rana-sylvatica/OFOF1/Standoffs/Sidewalls/ofof1-walls-3dprint-alt.STL

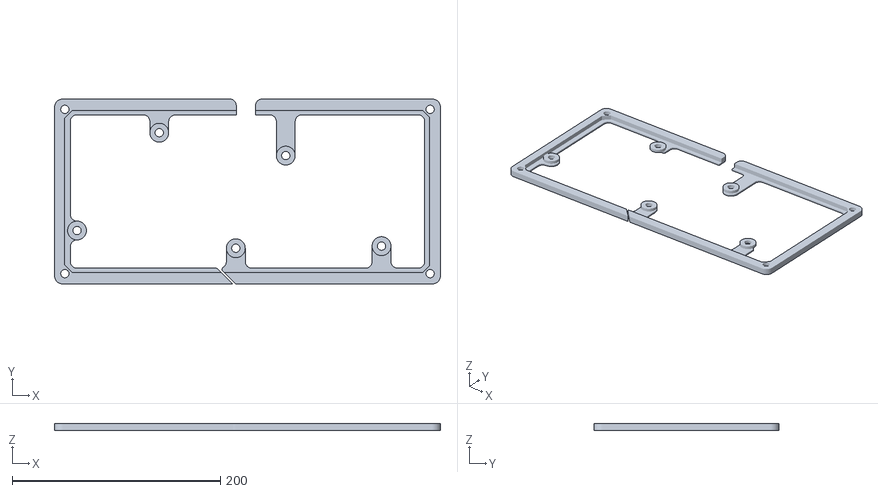
[picture p15: CAD file, 2022-10-11]
Standoffs/Sidewalls/ofof1-walls-3dprint-alt.STL
370.8 x 177.8 x 7.00
