rana-sylvatica/OFOF1/Standoffs/Top_standoff_short.STL

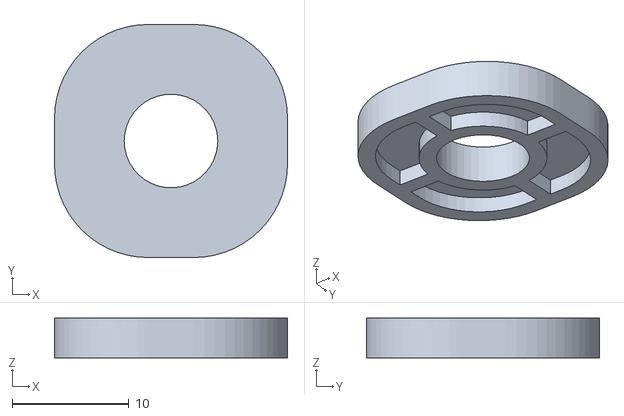
[picture p16: CAD file, 2022-07-05]
Standoffs/Top_standoff_short.STL
19.9 x 19.9 x 3.40
