rana-sylvatica/OFOF1/Standoffs/Sidewalls/ofof1-walls-JLC_acrylic.STL

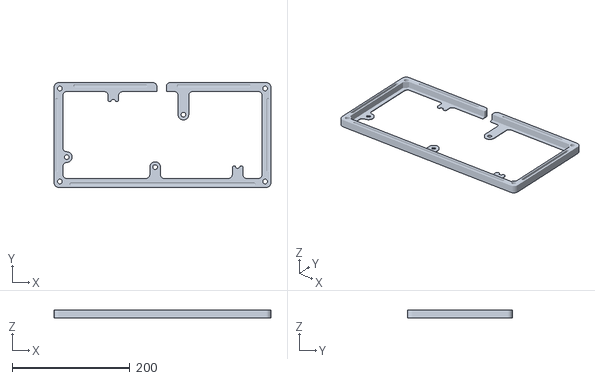
[picture p17: CAD file, 2022-10-11]
Standoffs/Sidewalls/ofof1-walls-JLC_acrylic.STL
368.3 x 177.8 x 13.0
