rana-sylvatica/OFOF1/Standoffs/Bottom_standoff_x10.STL

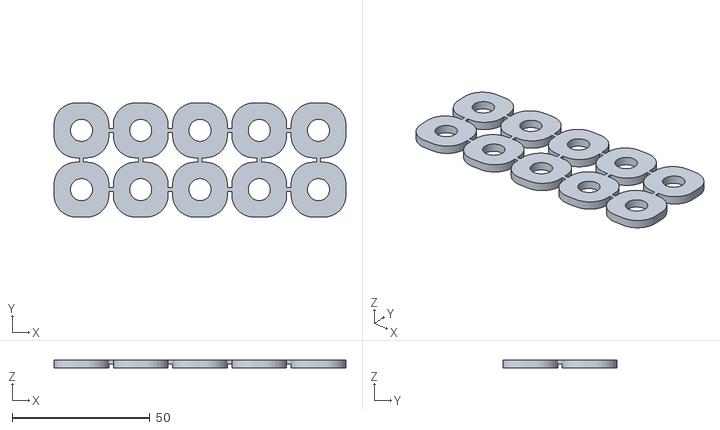
[picture p19: CAD file, 2022-07-05]
Standoffs/Bottom_standoff_x10.STL
105.9 x 41.4 x 3.00
