rana-sylvatica/OFOF1/Standoffs/Corner_standoff_tall_x8.STL

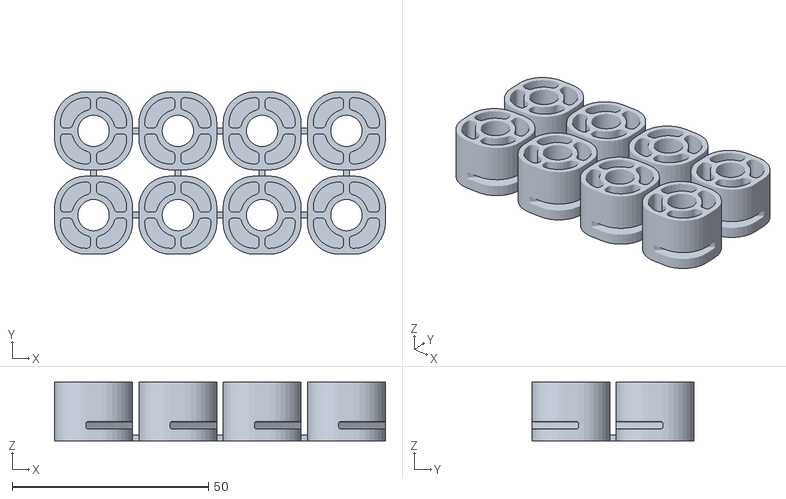
[picture p20: CAD file, 2022-07-05]
Standoffs/Corner_standoff_tall_x8.STL
84.4 x 41.4 x 15.0
