rana-sylvatica/OFOF1/Standoffs/Top_standoff_short_x10.STL

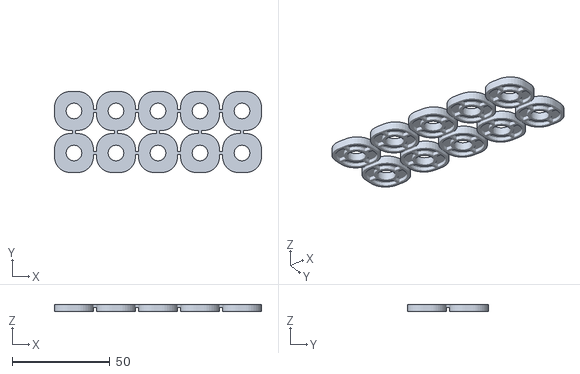
[picture p21: CAD file, 2022-07-05]
Standoffs/Top_standoff_short_x10.STL
105.9 x 41.4 x 3.40
