rana-sylvatica/OFOF1/Standoffs/Corner_standoff_short_x8.STL

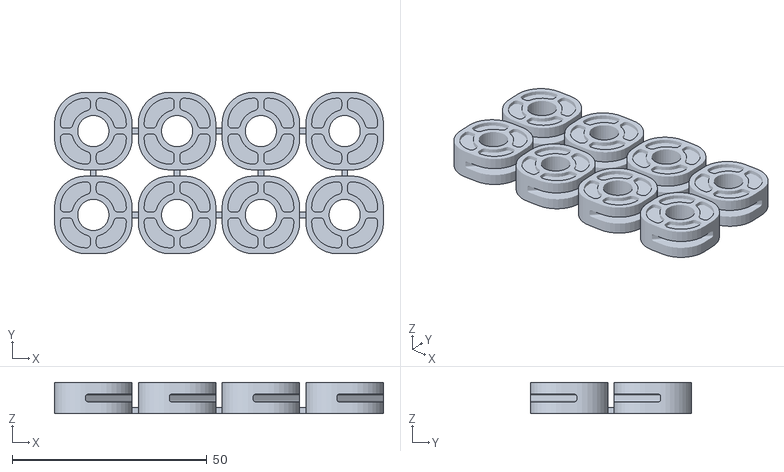
[picture p22: CAD file, 2022-07-05]
Standoffs/Corner_standoff_short_x8.STL
84.4 x 41.4 x 8.00
